sdebby/3NCRYP2P/media/IMG_9111.jpg

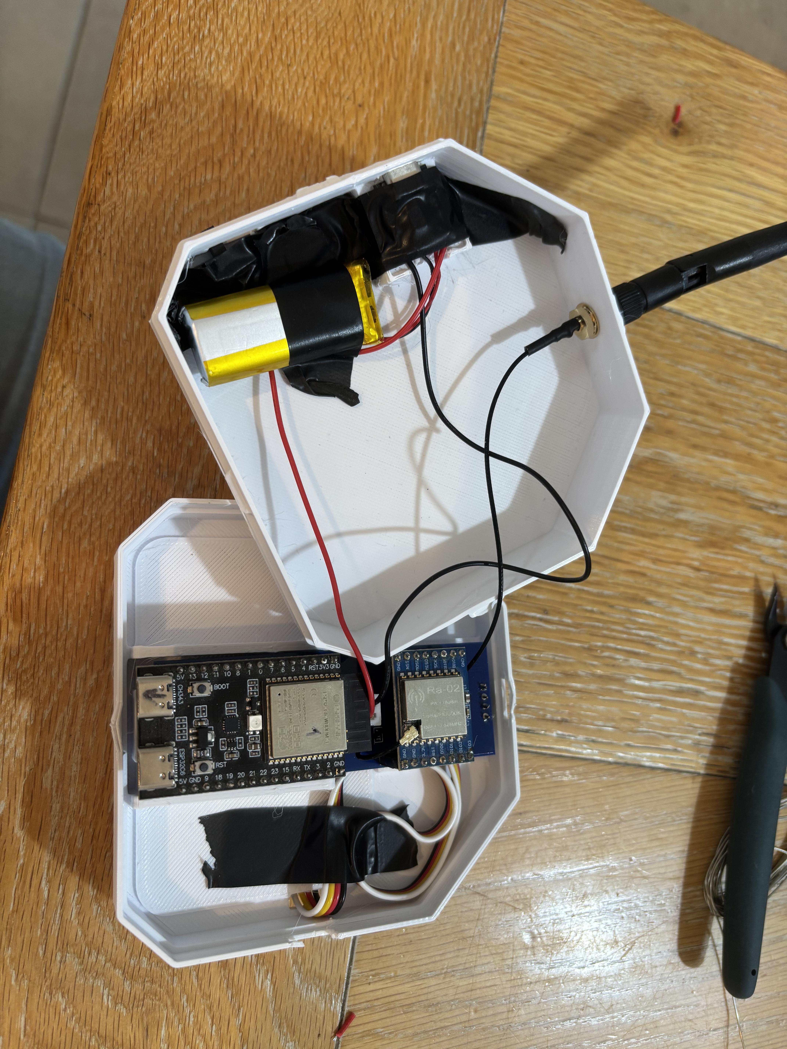
media/IMG_9111.jpg
